keyboardpartner/esim_8266/docs/EPROM-Simulator_PEPS_(1985-05)_GERMAN.pdf

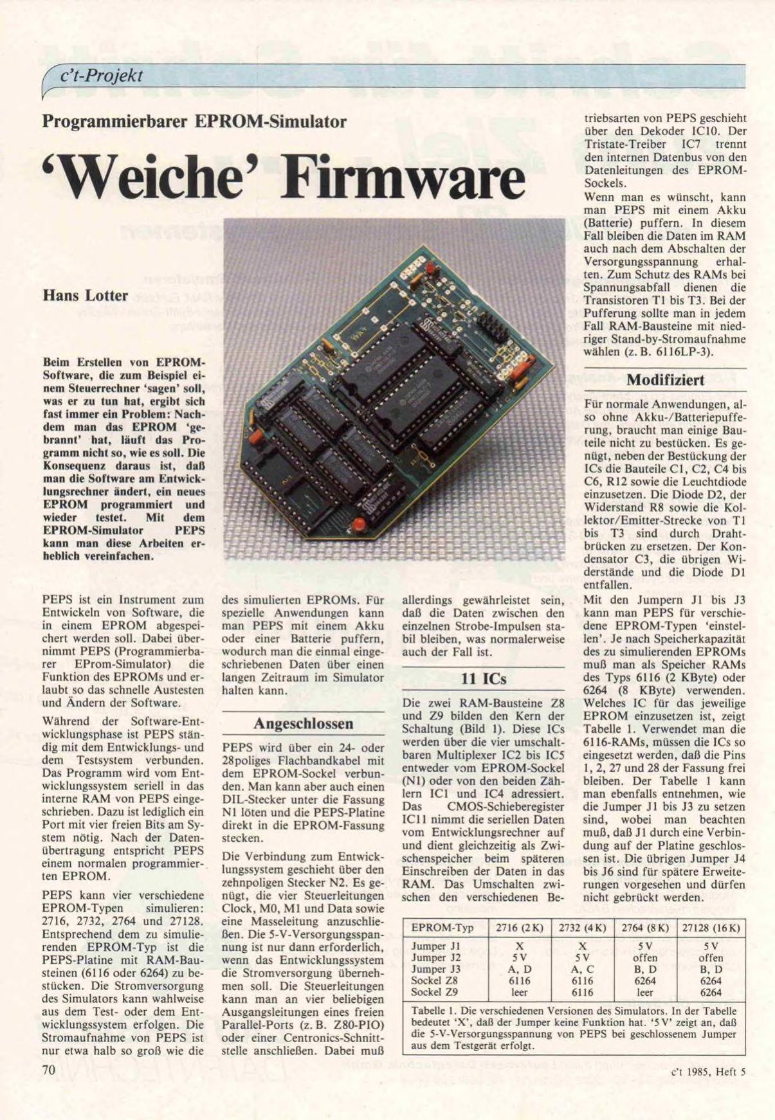
[picture p55: page 1]
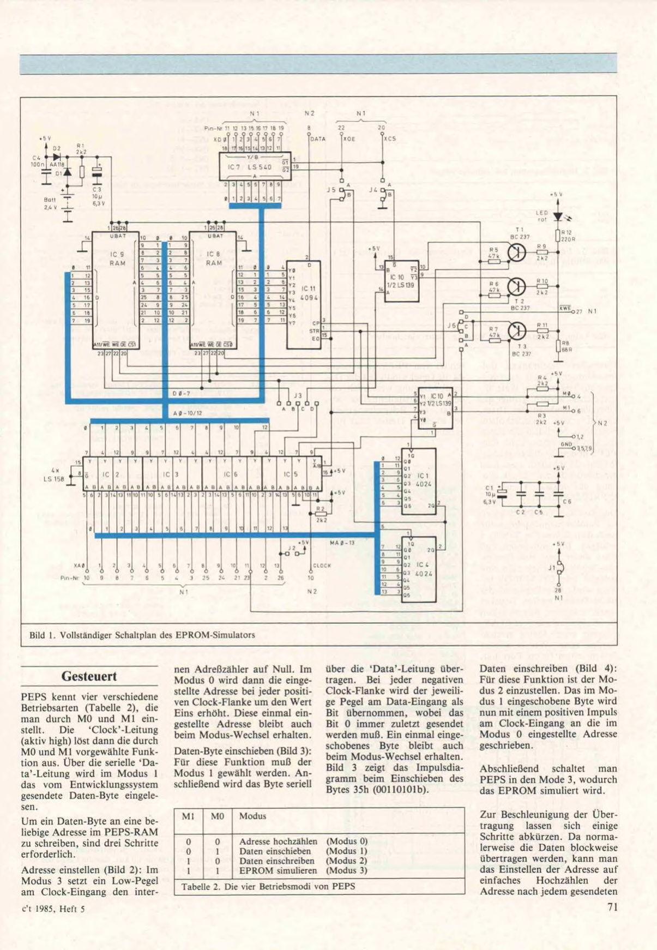
[picture p56: page 2]
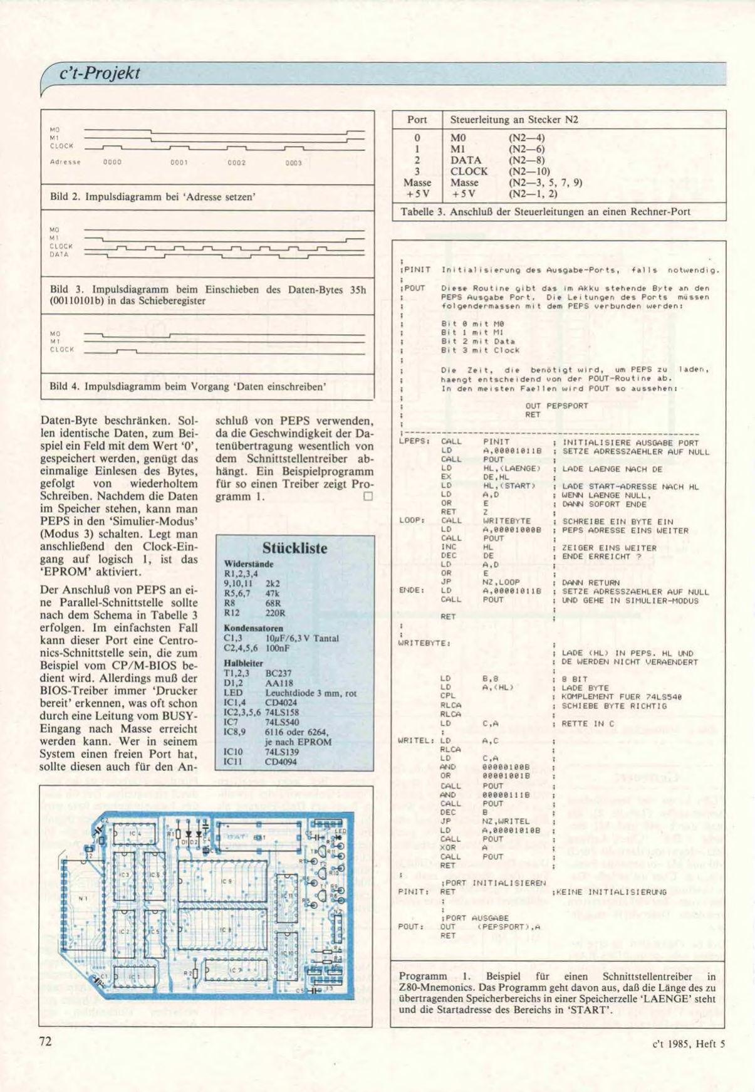
[picture p57: page 3]
