keyboardpartner/esim_8266/docs/2532-EPROM.gif

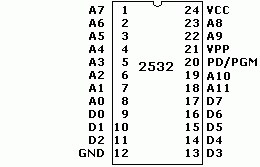
docs/2532-EPROM.gif
