keyboardpartner/esim_8266/docs/esim/pic02.jpg

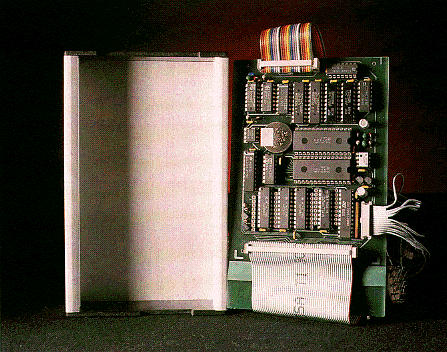
docs/esim/pic02.jpg
