keyboardpartner/esim_8266/docs/esim/pic04.jpg

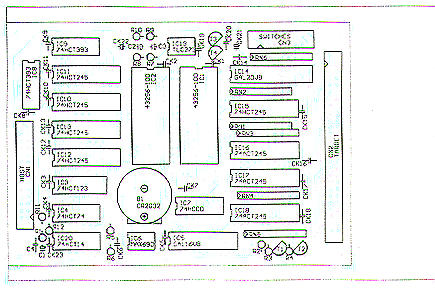
docs/esim/pic04.jpg
