keyboardpartner/esim_8266/pcb/MOJO/jtag_esp_simple_silk.pdf

D1
MD1

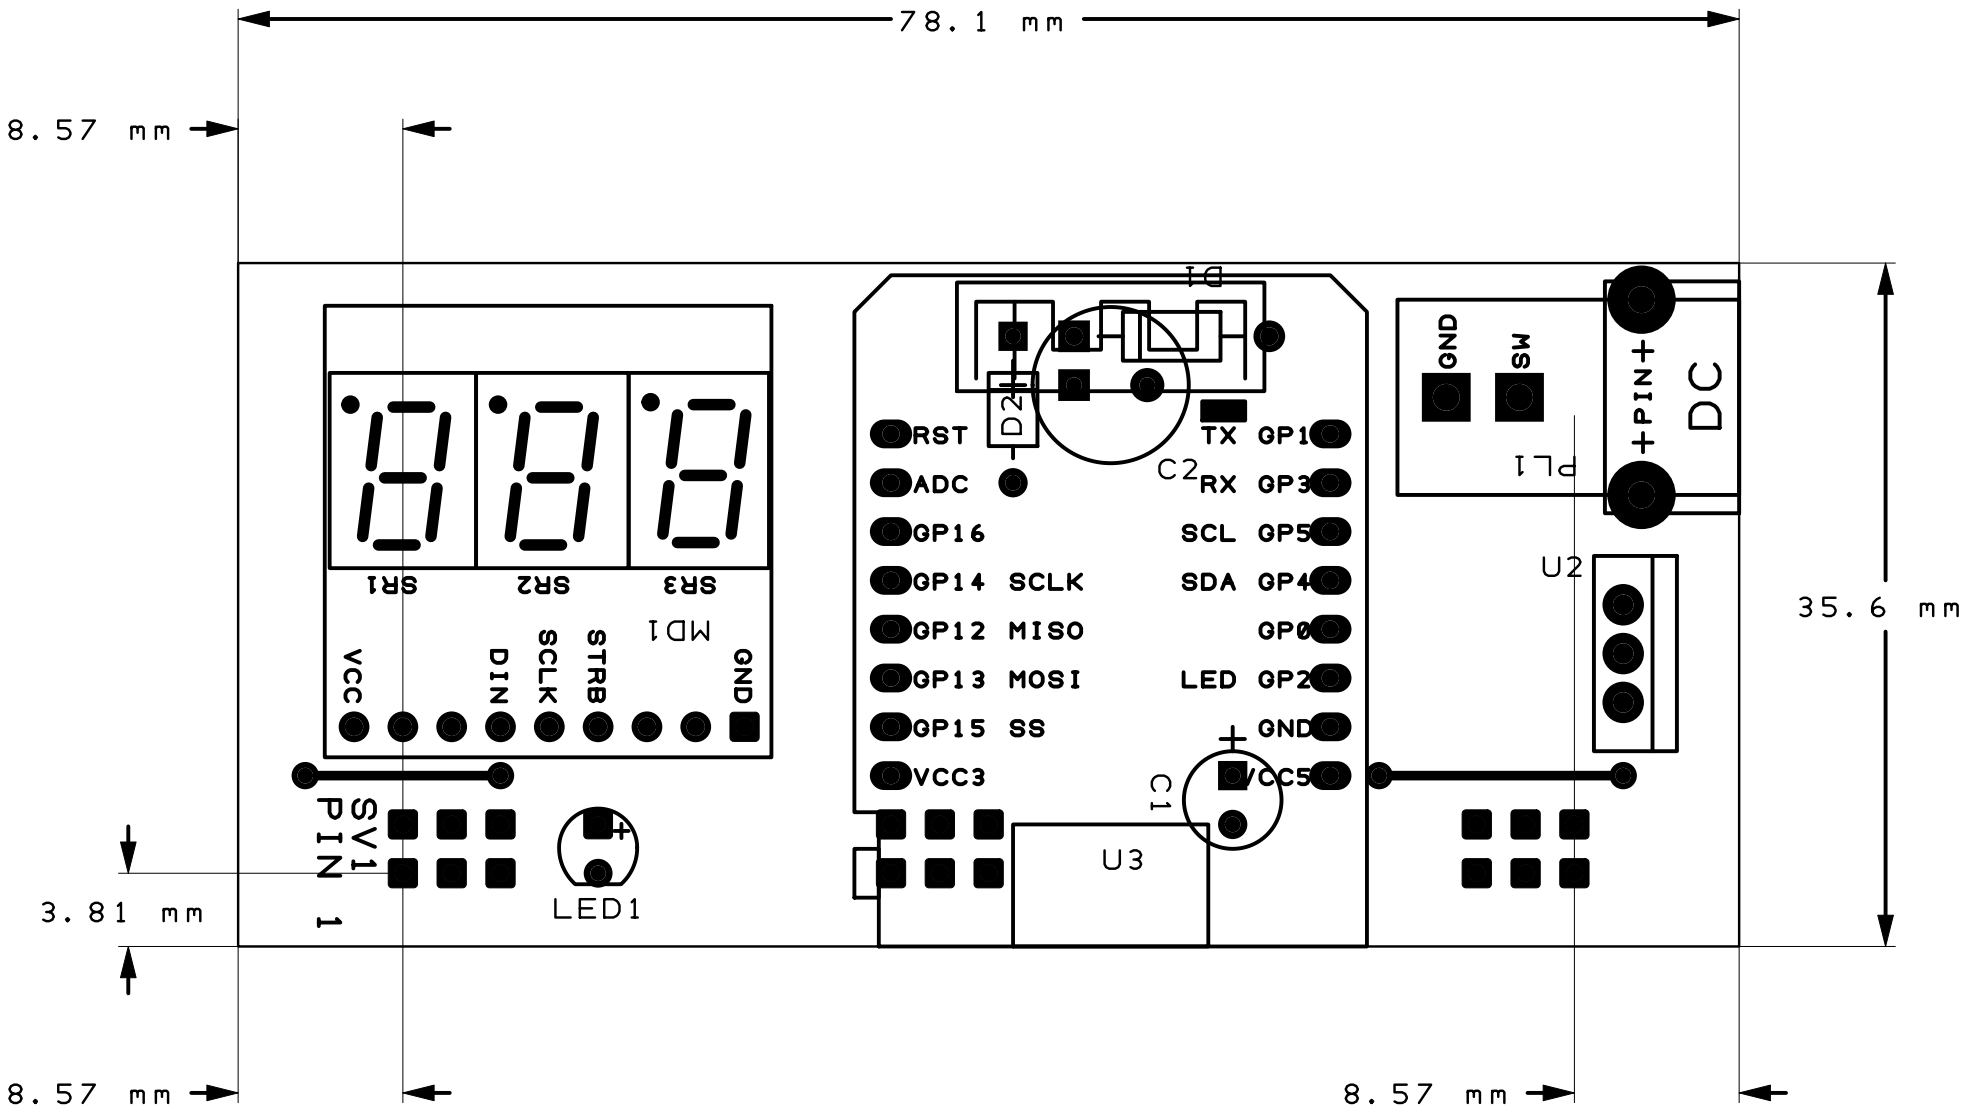
[picture p68: page 1]
LED1; LED1XZ1
