keyboardpartner/esim_8266/pcb/MOJO/jtag_esp_tft.pdf

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

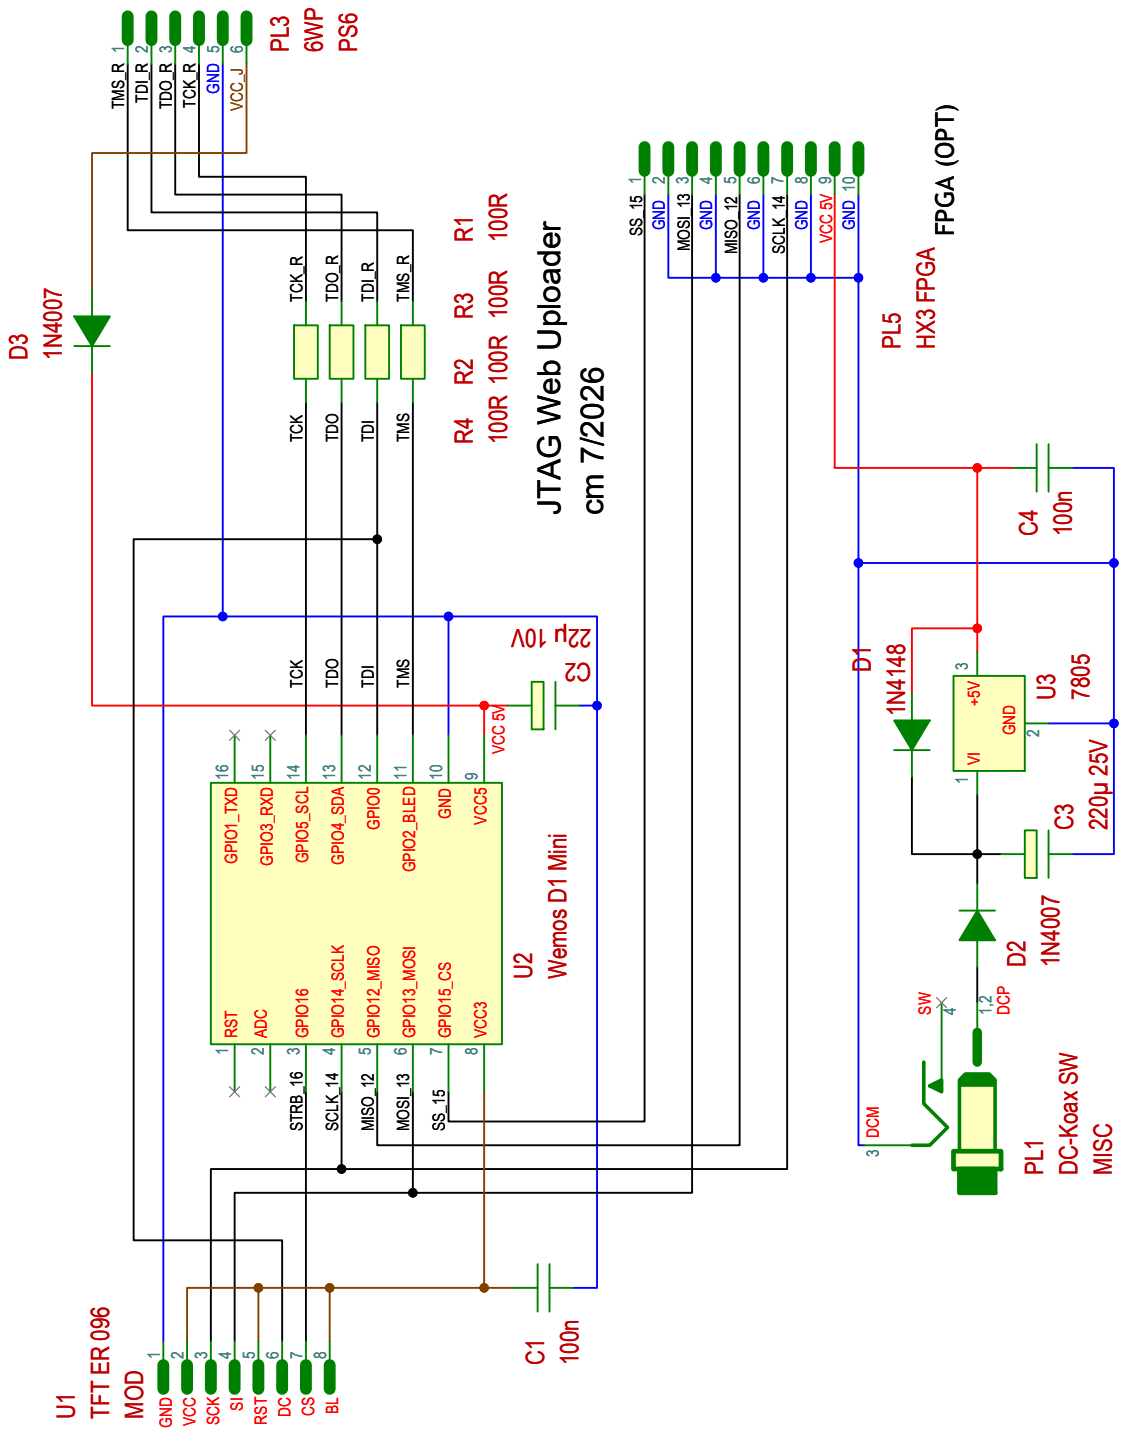
[picture p76: page 1]
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
