keyboardpartner/esim_8266/pcb/MOJO/jtag_esp_dil_cable_schem.pdf

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

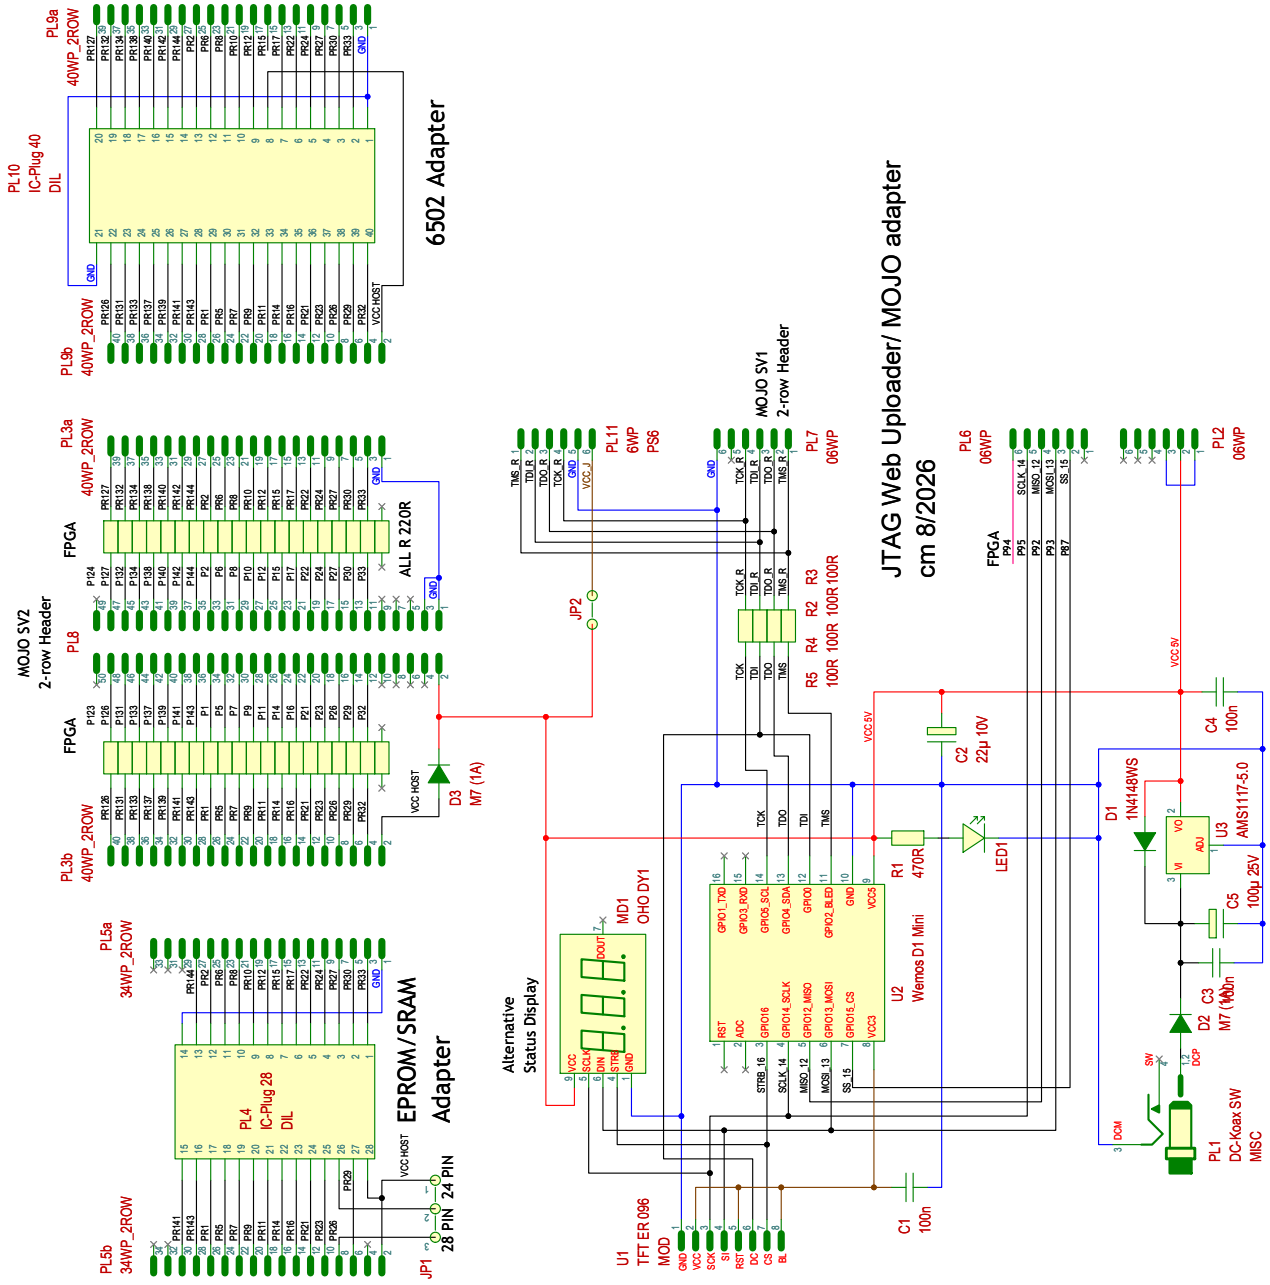
[picture p77: page 1]
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
