keyboardpartner/esim_8266/pcb/MOJO/jtag_esp_dil_cable_silk.pdf

PL4
PL5

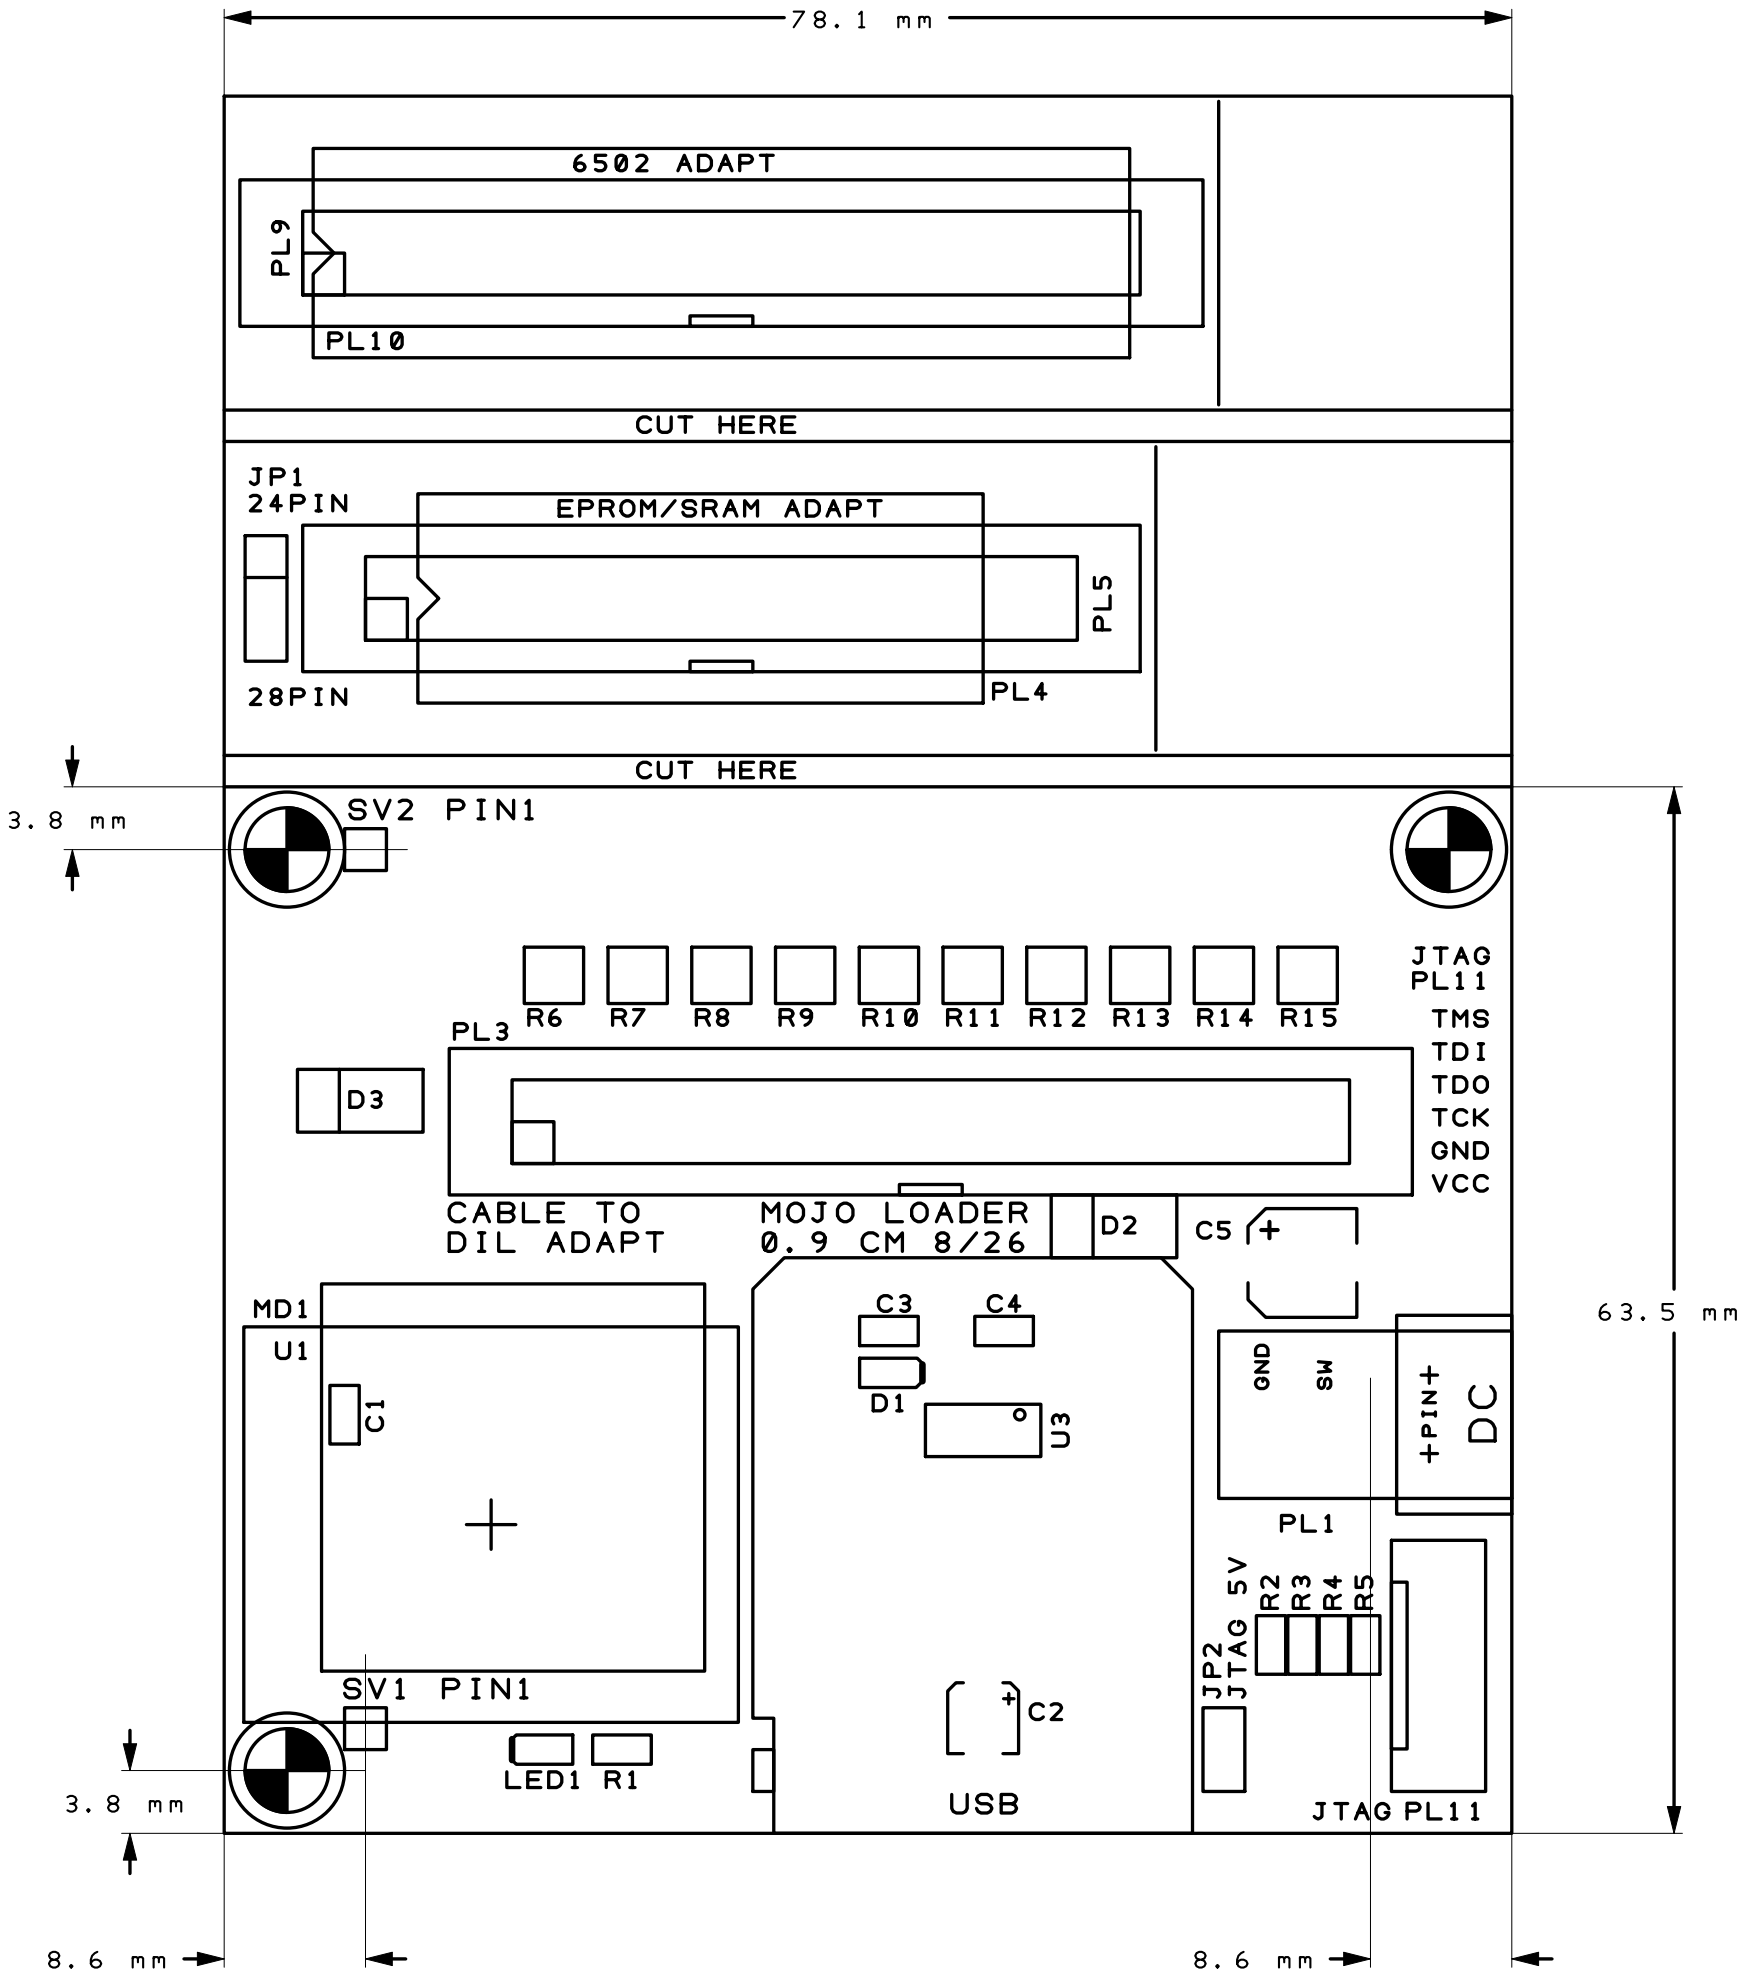
[picture p78: page 1]
