keyboardpartner/esim_8266/pcb/MOJO/jtag_esp_dil_cable_silk_btm.pdf

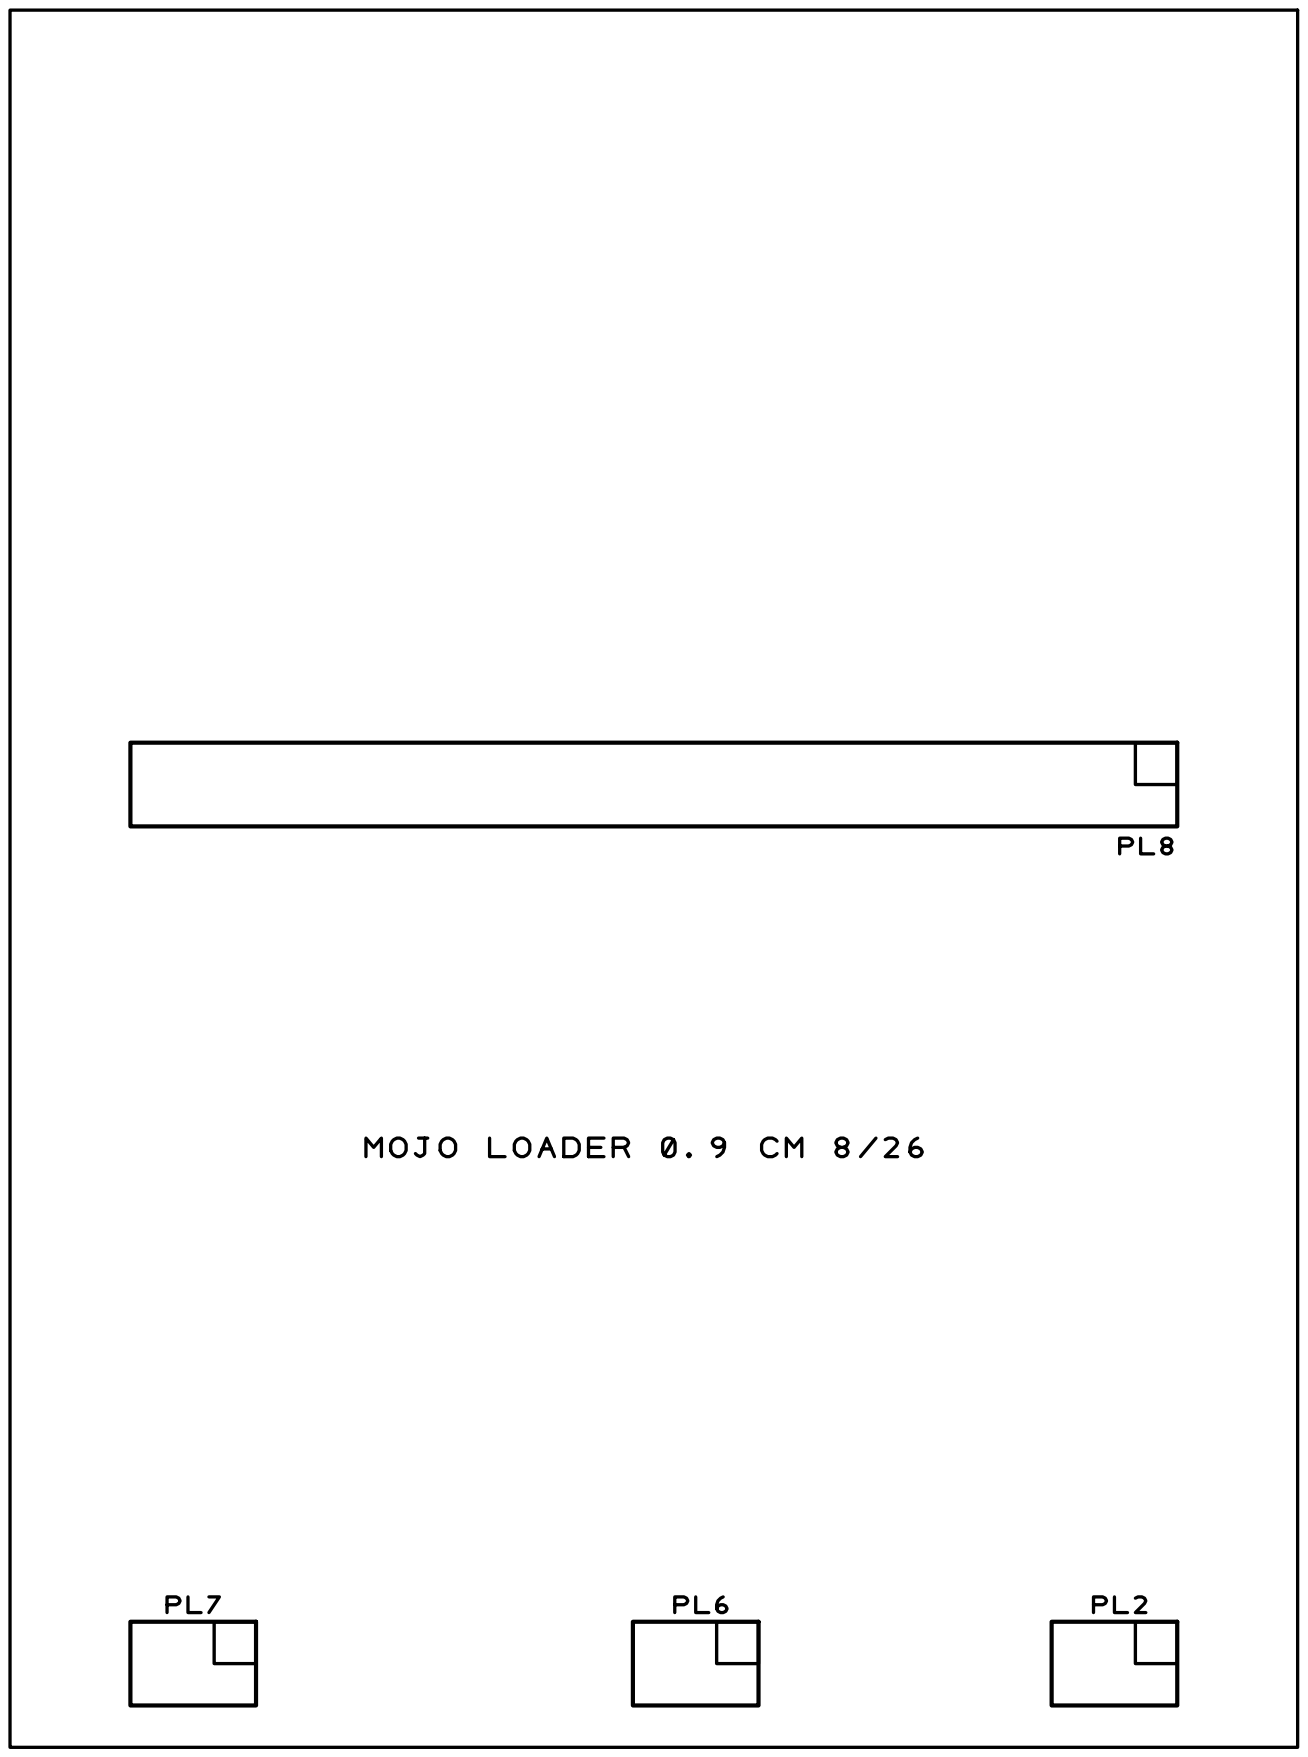
[picture p79: page 1]
