keyboardpartner/esim_8266/pcb/MOJO/mojo_eprom_adapter.pdf

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

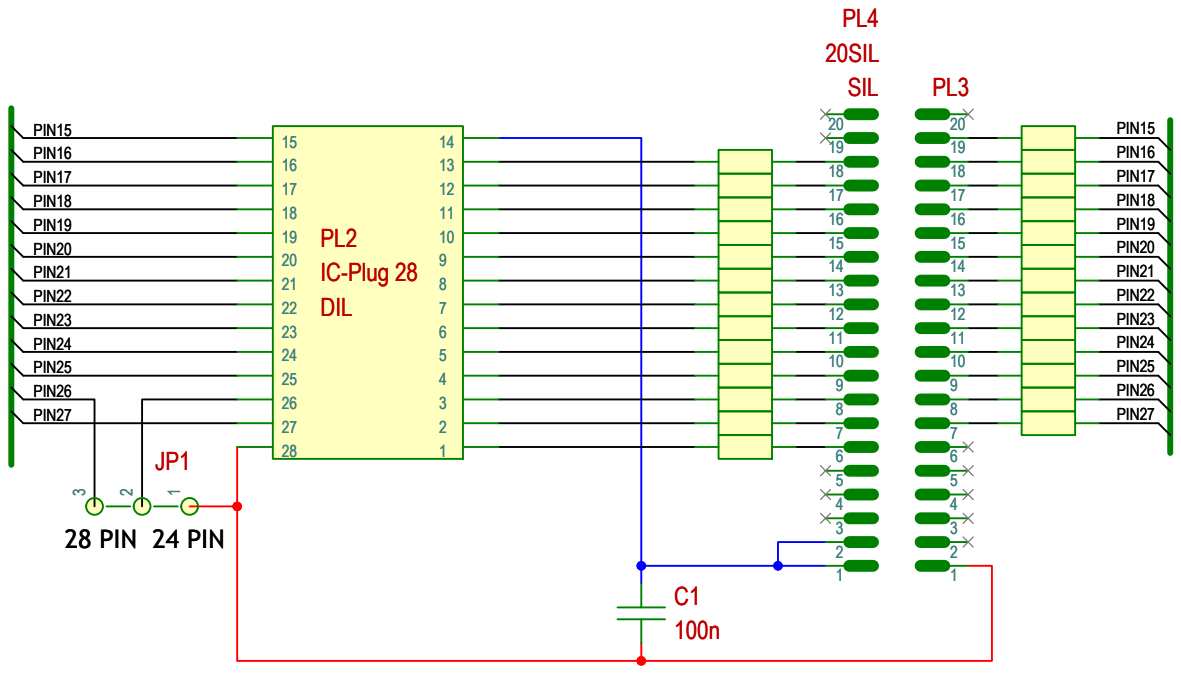
[picture p80: page 1]
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
