keyboardpartner/esim_8266/pcb/MOJO/jtag_esp_simple.pdf

D1
MD1

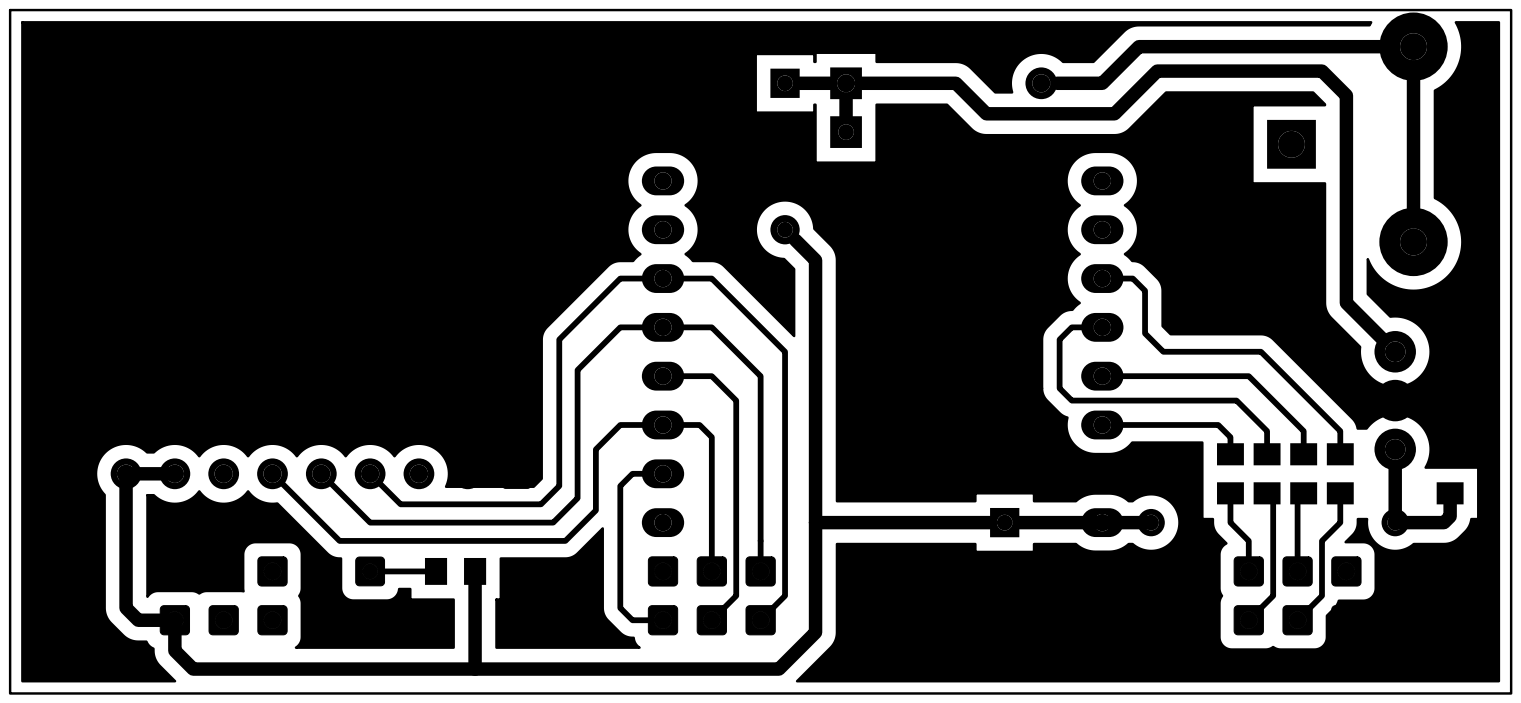
[picture p81: page 1]
