keyboardpartner/esim_8266/pcb/MOJO/jtag_esp_simple_botm.pdf

D1
MD1
