keyboardpartner/esim_8266/pcb/ESIM/esim_esp_pcb.pdf

PL2

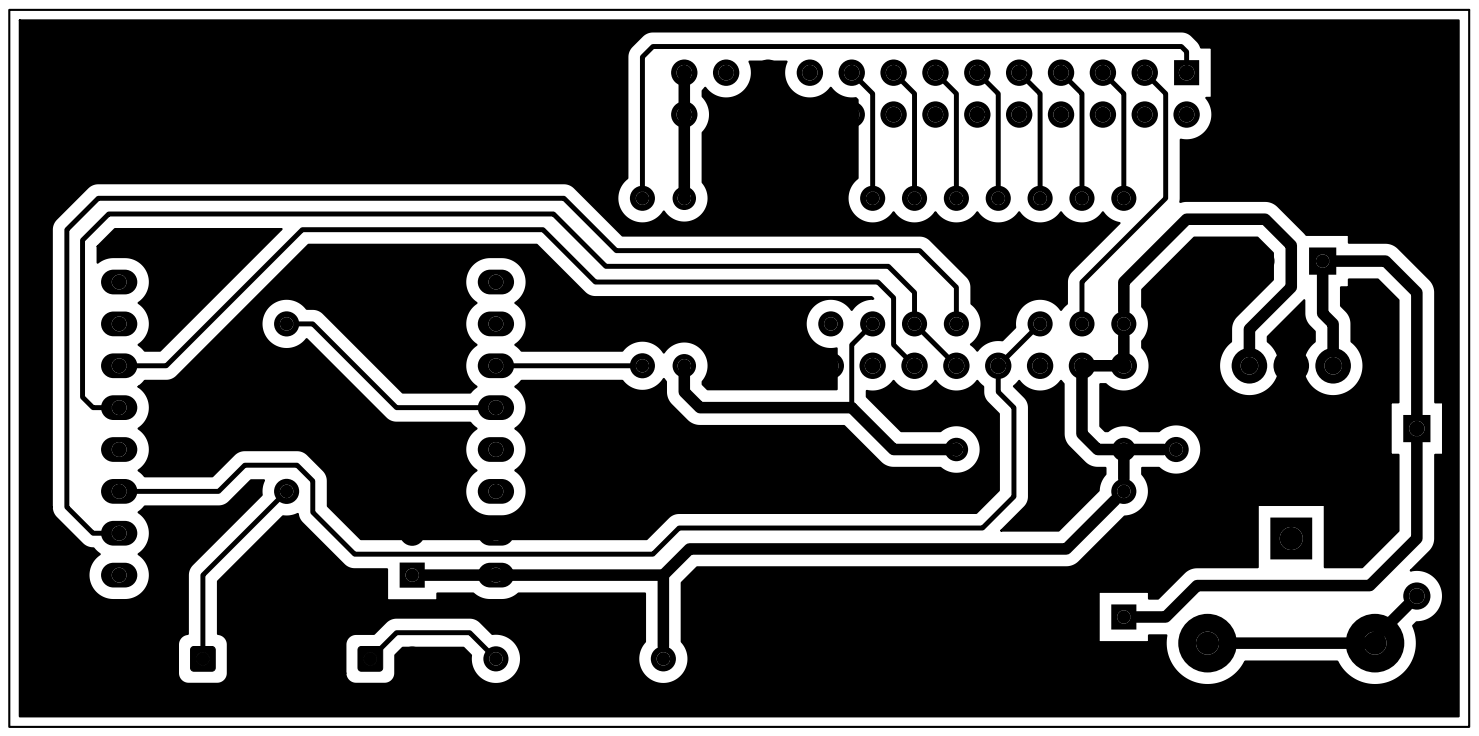
[picture p82: page 1]
