keyboardpartner/esim_8266/pcb/ESIM/esim_esp_silk.pdf

PL2

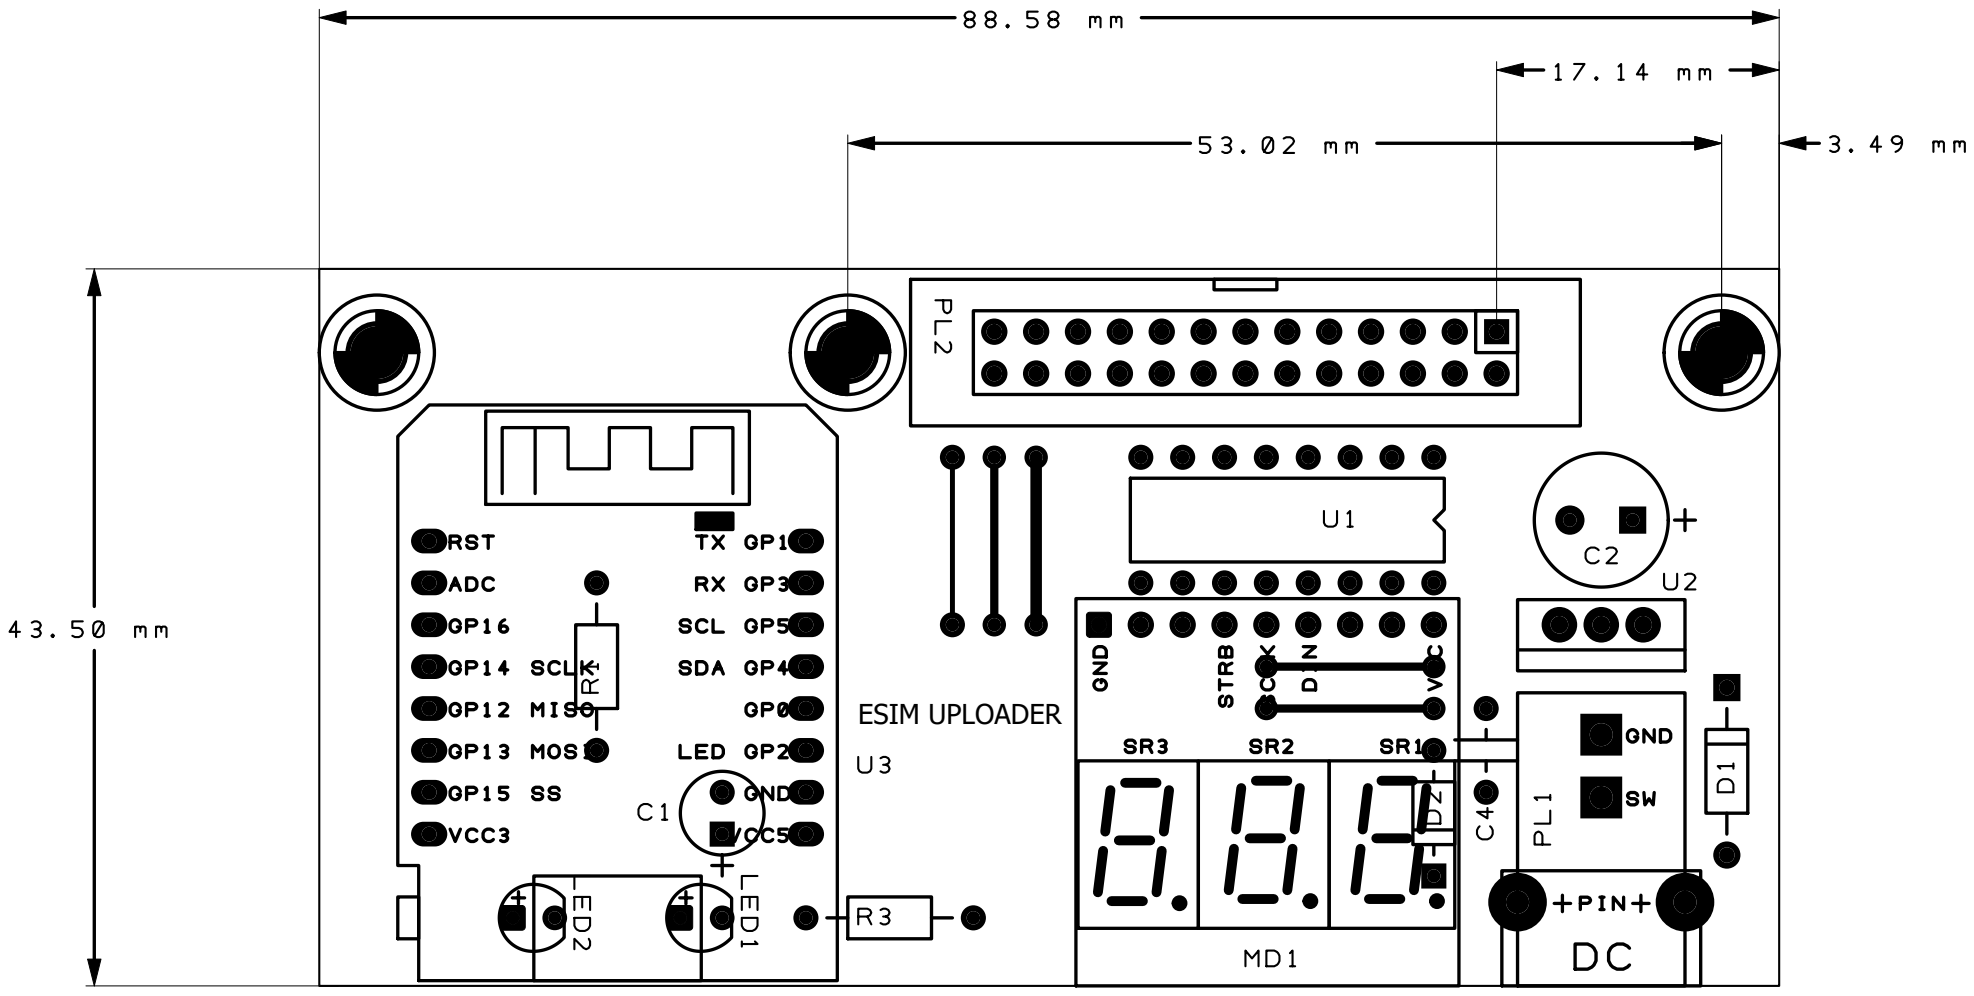
[picture p83: page 1]
