keyboardpartner/esim_8266/pcb/GODIL/godil_esp_silk.pdf

C1
MD1

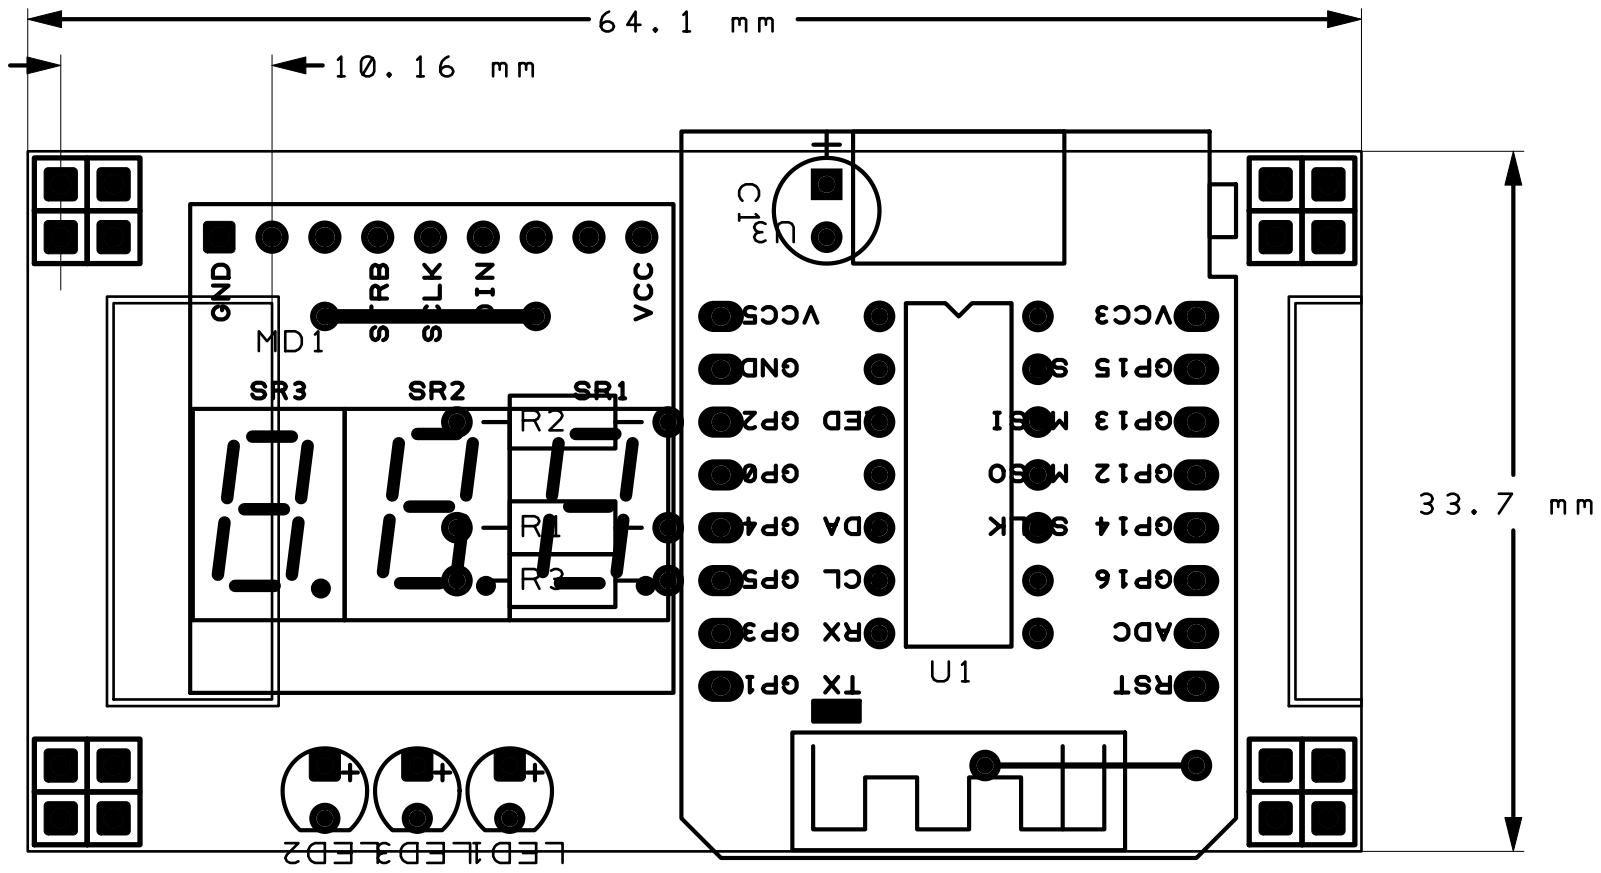
[picture p84: page 1]
