keyboardpartner/esim_8266/include/serial_cmd.h

#pragma once

// ##############################################################################
//
//      #####  ####### ######  ###    #    #           #####  #     # ######  
//     #     # #       #     #  #    # #   #          #     # ##   ## #     # 
//     #       #       #     #  #   #   #  #          #       # # # # #     # 
//      #####  #####   ######   #  #     # #          #       #  #  # #     # 
//           # #       #   #    #  ####### #          #       #     # #     # 
//     #     # #       #    #   #  #     # #          #     # #     # #     # 
//      #####  ####### #     # ### #     # #######     #####  #     # ######  
//                                                                                    
// ##############################################################################
// SERIAL COMMANDS
// ##############################################################################


// ##############################################################################
//
//     ### #     # ####### #######    #     # ####### #       ######  
//      #  ##    # #       #     #    #     # #       #       #     # 
//      #  # #   # #       #     #    #     # #       #       #     # 
//      #  #  #  # #####   #     #    ####### #####   #       ######  
//      #  #   # # #       #     #    #     # #       #       #       
//      #  #    ## #       #     #    #     # #       #       #       
//     ### #     # #       #######    #     # ####### ####### #       
//                                                                                  
// ##############################################################################
// SERIAL INFO AND HELP TEXT
// ##############################################################################

#include <Arduino.h>

void printIDcode() {
  #ifdef JTAG_SPARTAN6
    Serial.println("");
    printCenteredSerial(F("FPGA Info"));
    jtagCheckIDcode();
    Serial.printf("ID code: %08X\n", jtagIDcode);
    // Check for Xilinx ID code 0x0093 and print success or error message
    if (fpgaValid && fpgaConfigured) {
      Serial.println(F("FPGA configured successfully."));
    } else {
      Serial.println(F("FPGA configuration failed."));
      dy1message(F("Err"));
      drawMsgBox(F("FPGA"), F("ID Error"), DB_ERROR);
    }
    fpgaVersion = getFPGAversion();
    if ((fpgaVersion == 0xFFFFFFFF) || (fpgaVersion == 0x00000000)) {
      Serial.println(F("FPGA version read failed."));
      dy1message(F("Err"));
      drawMsgBox(F("FPGA"), F("Version Err"), DB_ERROR);
    } else {
      Serial.printf("FPGA version: %08X\n", fpgaVersion);
    }
    Serial.print(F("Emulation: "));
    Serial.println(kChipTypeNames[currentChipTypeIndex]);
    printDivLine();
   #endif
}

void printFileInfo() {
  const bool stagedExists = fsMounted && currentFilePath.length() > 0 && LittleFS.exists(currentFilePath);
  Serial.println("");
  printCenteredSerial(F("File Info"));
  Serial.print(F("LittleFS mounted: "));
  Serial.println(fsMounted ? F("Yes") : F("No"));
  Serial.print(F("FPGA Config: "));
  Serial.println(startupFpgaPath.length() ? startupFpgaPath : String(F("none")));
  Serial.print(F("Stream File: "));
  Serial.print(currentFilePath.length() ? currentFilePath : String(F("none")));
  Serial.println(stagedExists ? F(" OK") : F(" not found"));
  Serial.print(F("Start Addr: "));
  Serial.println(lastUploadStartAddr);
  Serial.print(F("Length: "));
  Serial.println(stagedFileBytes);
  printDivLine();
}

// Lists all LittleFS root directory entries on serial.
void listLittleFsEntries() {
  Serial.println("");
  if (!fsMounted) {
    Serial.println(F("ERROR: filesystem not mounted."));
    return;
  }
  Dir dir = LittleFS.openDir("/");
  size_t entryCount = 0;
  size_t totalBytes = 0;

  printCenteredSerial(F("Directory Info"));
  while (dir.next()) {
    const String path = normalizeFsPath(dir.fileName());
    const size_t bytes = dir.fileSize();
    Serial.print(path);
    Serial.print(F(" ("));
    Serial.print(bytes);
    Serial.println(F(" bytes)"));
    ++entryCount;
    totalBytes += bytes;
    delay(0); yield();
  }
  if (entryCount == 0) {
    Serial.println(F("  <empty>"));
  }
  Serial.print(F("Entries: "));
  Serial.print(entryCount);
  Serial.print(F(", total bytes: "));
  Serial.println(totalBytes);
  printDivLine();
}

void printWebInfo() {
  Serial.println("");
  printCenteredSerial(F("WiFi Info"));
  Serial.print(F("Wi-Fi mode: "));
  Serial.println(wifiModeLabel);
  Serial.print(F("Wi-Fi STA SSID: "));
  Serial.println(staSsid.length() ? staSsid : String(F("<empty>")));
  Serial.print(F("IP address: "));
  Serial.println(wifiIpAddress);
  Serial.print(F("AP SSID: "));
  Serial.println(kApSsid);
  printDivLine();
}


// ##############################################################################
//
//     #     # ####### #       ######  ####### ######   #####  
//     #     # #       #       #     # #       #     # #     # 
//     #     # #       #       #     # #       #     # #       
//     ####### #####   #       ######  #####   ######   #####  
//     #     # #       #       #       #       #   #         # 
//     #     # #       #       #       #       #    #  #     # 
//     #     # ####### ####### #       ####### #     #  #####  
//                                                                                    
// ##############################################################################
// SERIAL COMMAND HELPER FUNCTIONS
// ##############################################################################
                                                          
#if defined(GODIL_SPI) || defined(JTAG_SPARTAN6)
void hexdumpInputBytes256(uint32_t startAddr) {
  // Hex dump 256 bytes from device starting at startAddr.
  startBlockTransfer(startAddr);
  for (uint16_t rowStart = 0; rowStart < 256; rowStart += 16) {
    char line[96];
    int lineLen = snprintf(line, sizeof(line), "%06lX: ", static_cast<unsigned long>(startAddr + rowStart));
    for (uint8_t i = 0; i < 16; ++i) {
      const uint8_t value = inputByte();
      lineLen += snprintf(line + lineLen, sizeof(line) - lineLen, "%02X ", value);
    }

    if (lineLen > 0 && line[lineLen - 1] == ' ') {
      line[lineLen - 1] = '\0';
    }
    Serial.println(line);

    if ((rowStart & 0x007F) == 0) {
      delay(0); yield();
    }
  }
  stopBlockTransfer();
}
#endif

void printSerialCommandsInfo() {
  Serial.println("");
  printCenteredSerial(F("Serial Commands"));
  #ifdef JTAG_SPARTAN6
    Serial.println(F("c: Configurate FPGA with last/staged .bit file"));
    Serial.println(F("o: List chip types and select emulation mode"));
  #endif
  #if defined(GODIL_SPI) || defined(JTAG_SPARTAN6)
    Serial.println(F("d<start><CR>: Hexdump of 256 bytes from device"));
    Serial.println(F("j<filename,start,len><CR>: dump EPROM to file"));
  #endif
  Serial.println(F("e: Erase EPROM"));
  Serial.println(F("h: Print web/status info and this help text"));
  Serial.println(F("i: Print file debug info"));
  Serial.println(F("l: List LittleFS directory entries"));
  Serial.println(F("t: Test SPI transfer"));
  Serial.println(F("r: Replay last/staged file"));
  printDivLine();
  Serial.println(F("a<start><CR>: Set start address for next serial upload"));
  Serial.println(F("n<filename><CR>: Set filename for next serial upload"));
  Serial.println(F("u<lenLo><lenHi><data...><cksLo><cksHi>: Framed binary upload"));
  Serial.println(F("x: Print \"Ready.\" for handshaking with serial uploader"));
  printDivLine();
  Serial.println(F("w<ssid><CR>: Set STA Wi-Fi SSID"));
  Serial.println(F("p<password><CR>: Set STA Wi-Fi password"));
  Serial.println();
  Serial.println(F("Note: start/len accept decimal or 0x-prefixed hex"));
  printDivLine();
}  

// Reads one serial byte with timeout to support robust framed transfers.
bool readSerialByteWithTimeout(uint8_t &outByte, uint32_t timeoutMs) {
  const uint32_t startMs = millis();
  while ((millis() - startMs) < timeoutMs) {
    if (Serial.available() > 0) {
      outByte = static_cast<uint8_t>(Serial.read());
      return true;
    }
    delay(0); yield();
  }
  return false;
}

// Reads an ASCII filename terminated by CR for the next serial upload.
bool readSerialFilename(String &filenameOut) {
  String rawName;
  while (true) {
    uint8_t nextByte = 0;
    if (!readSerialByteWithTimeout(nextByte, kSerialUploadTimeoutMs*25U)) {
      return false;
    }
    if (nextByte == '\r') {
      filenameOut = sanitizeUploadFilename(rawName);
      return true;
    }
    if (nextByte == '\n') {
      continue;
    }
    rawName += static_cast<char>(nextByte);
    if (rawName.length() > kMaxFsPathLength * 2) {
      rawName.remove(kMaxFsPathLength * 2);
    }
  }
}

// Reads one ASCII line terminated by CR from serial input.
bool readSerialLine(String &lineOut, uint32_t timeoutMs) {
  String line;
  while (true) {
    uint8_t nextByte = 0;
    if (!readSerialByteWithTimeout(nextByte, timeoutMs)) {
      return false;
    }
    if (nextByte == '\r') {
      lineOut = line;
      return true;
    }
    if (nextByte == '\n') {
      continue;
    }
    line += static_cast<char>(nextByte);
    if (line.length() > 128) {
      line.remove(128);
    }
  }
}

// Parses decimal or 0x-prefixed hexadecimal unsigned values.
bool parseUnsignedValue(const String &text, uint32_t &valueOut) {
  String token = text;
  token.trim();
  if (token.length() == 0) {
    return false;
  }
  char *endPtr = nullptr;
  const unsigned long parsed = std::strtoul(token.c_str(), &endPtr, 0);
  if (endPtr == token.c_str() || *endPtr != '\0') {
    return false;
  }
  valueOut = static_cast<uint32_t>(parsed);
  return true;
}

// Parses serial dump command format: filename,start,len
bool parseDumpCommandArgs(const String &line, String &filenameOut, uint32_t &startAddrOut,
                          uint16_t &lenOut) {
  String argLine = line;
  argLine.trim();
  const int comma1 = argLine.indexOf(',');
  const int comma2 = (comma1 >= 0) ? argLine.indexOf(',', comma1 + 1) : -1;
  if (comma1 <= 0 || comma2 <= comma1 + 1) {
    return false;
  }
  const String filenameRaw = argLine.substring(0, comma1);
  const String startRaw = argLine.substring(comma1 + 1, comma2);
  const String lenRaw = argLine.substring(comma2 + 1);

  uint32_t parsedStart = 0;
  uint32_t parsedLen = 0;
  if (!parseUnsignedValue(startRaw, parsedStart) || !parseUnsignedValue(lenRaw, parsedLen)) {
    return false;
  }
  if (parsedLen == 0 || parsedLen > 0xFFFFUL) {
    return false;
  }
  String cleanName = sanitizeUploadFilename(filenameRaw);
  if (cleanName.length() == 0) {
    return false;
  }
  filenameOut = cleanName;
  startAddrOut = parsedStart;
  lenOut = static_cast<uint16_t>(parsedLen);
  return true;
}

                                                    
// ##############################################################################
//
//     #     # ######  #       #######    #    ######  
//     #     # #     # #       #     #   # #   #     # 
//     #     # #     # #       #     #  #   #  #     # 
//     #     # ######  #       #     # #     # #     # 
//     #     # #       #       #     # ####### #     # 
//     #     # #       #       #     # #     # #     # 
//      #####  #       ####### ####### #     # ######  
//                                                                                    
// ##############################################################################
// Handles serial upload command.
// ##############################################################################


// Usage: 'u' + lenLo,lenHi + payload + cksLo,cksHi; ACK after len, each 128B, checksum.
void processSerialUploadCommand() {
  if (!fsMounted) {
    Serial.println(F("ERROR: filesystem not mounted."));
    return;
  }

  uint8_t lenLo = 0;
  uint8_t lenHi = 0;
  if (!readSerialByteWithTimeout(lenLo, kSerialUploadTimeoutMs) ||
      !readSerialByteWithTimeout(lenHi, kSerialUploadTimeoutMs)) {
    Serial.write(kSerialNakByte);
    Serial.println(F("ERROR: timeout while reading length word."));
    return;
  }

  const uint16_t payloadLength = static_cast<uint16_t>(lenLo) |
                                 (static_cast<uint16_t>(lenHi) << 8);
  if (payloadLength == 0) {
    Serial.println(F("ERROR: payload length is zero."));
    return;
  }

  if (payloadLength > kMaxBytesToTransfer[currentChipTypeIndex]) {
    Serial.print(F("ERROR: payload exceeds limit "));
    Serial.println(kMaxBytesToTransfer[currentChipTypeIndex]);
    return;
  }

  // ACK command and length word, signaling sender to start payload transmission.
  Serial.write(kSerialAckByte);

  if (uploadStagingFile) {
    uploadStagingFile.close();
  }
  currentUploadFsError = false;
  uploadInProgress = true;
  setUploadLed(true);
  const String requestedFilename = pendingSerialFilename;
  pendingSerialFilename = String();
  if (requestedFilename.length() > 0) {
    currentFilePath = makeWebUploadFilePath(requestedFilename);
    lastFilename = requestedFilename;
  } else {
    currentFilePath = makeWebUploadFilePath(F("serial_upload.bin"));
    lastFilename = baseNameFromPath(currentFilePath);
  }
  DPRINT(F("Serial upload path: "));
  DPRINTLN(currentFilePath);
  stagedFileBytes = 0;
  streamOffset = 0;
  clearDataBus();

  LittleFS.remove(currentFilePath);
  uploadStagingFile = LittleFS.open(currentFilePath, "w");
  if (!uploadStagingFile) {
    currentUploadFsError = true;
    uploadInProgress = false;
    setUploadLed(false);
    Serial.println(F("ERROR: failed to open staging file."));
    return;
  }

  uint16_t calculatedChecksum = 0;

  for (uint16_t i = 0; i < payloadLength; ++i) {
    uint8_t dataByte = 0;
    if (!readSerialByteWithTimeout(dataByte, kSerialUploadTimeoutMs)) {
      uploadStagingFile.close();
      LittleFS.remove(currentFilePath);
      stagedFileBytes = 0;
      lastFileBytes = 0;
      currentUploadFsError = true;
      uploadInProgress = false;
      setUploadLed(false);
      Serial.write(kSerialNakByte);
      Serial.println(F("ERROR: timeout waiting for data byte."));
      return;
    }

    const size_t written = uploadStagingFile.write(&dataByte, 1);
    if (written != 1) {
      uploadStagingFile.close();
      LittleFS.remove(currentFilePath);
      stagedFileBytes = 0;
      lastFileBytes = 0;
      currentUploadFsError = true;
      uploadInProgress = false;
      setUploadLed(false);
      Serial.println(F("ERROR: write failed."));
      return;
    }

    ++stagedFileBytes;
    calculatedChecksum = static_cast<uint16_t>(calculatedChecksum + dataByte);

    const uint16_t receivedBytes = static_cast<uint16_t>(i + 1);
    if ((receivedBytes % kSerialAckChunkBytes) == 0 || receivedBytes == payloadLength) {
      Serial.write(kSerialAckByte);
    }

    if ((i & 0x1F) == 0) {
      delay(0); yield();
    }
  }

  uint8_t cksLo = 0;
  uint8_t cksHi = 0;
  if (!readSerialByteWithTimeout(cksLo, kSerialUploadTimeoutMs) ||
      !readSerialByteWithTimeout(cksHi, kSerialUploadTimeoutMs)) {
    uploadStagingFile.close();
    LittleFS.remove(currentFilePath);
    stagedFileBytes = 0;
    lastFileBytes = 0;
    currentUploadFsError = true;
    uploadInProgress = false;
    setUploadLed(false);
    Serial.write(kSerialNakByte);
    Serial.println(F("ERROR: timeout while reading checksum word."));
    return;
  }

  const uint16_t receivedChecksum = static_cast<uint16_t>(cksLo) |
                                    (static_cast<uint16_t>(cksHi) << 8);

  if (receivedChecksum != calculatedChecksum) {
    uploadStagingFile.close();
    LittleFS.remove(currentFilePath);
    stagedFileBytes = 0;
    lastFileBytes = 0;
    currentUploadFsError = true;
    uploadInProgress = false;
    setUploadLed(false);
    Serial.write(kSerialNakByte);
    Serial.print(F("ERROR: checksum mismatch, expected="));
    Serial.print(calculatedChecksum);
    Serial.print(F(", received="));
    Serial.println(receivedChecksum);
    return;
  }

  // ACK checksum receipt only when checksum is valid.
  Serial.write(kSerialAckByte);

  uploadStagingFile.close();
  lastFileBytes = stagedFileBytes;
  uploadInProgress = false;
  setUploadLed(false);
  lastFilename = baseNameFromPath(currentFilePath);
  // lastUploadStartAddr is already set when processing the 'a' command.
  if (isBitstreamFilePath(currentFilePath)) {
    startupFpgaPath = normalizeFsPath(currentFilePath);
    lastUploadStartAddr = 0;
  }
  if (!saveFileSettingsForFile(currentFilePath, lastUploadStartAddr)) {
    Serial.println(F("ERROR: failed to save file settings metadata."));
  }
  if (!saveGlobalSettings()) {
    Serial.println(F("ERROR: failed to save global settings."));
  }
  if (!startPlaybackFromStaging(lastUploadStartAddr, currentFilePath)) {
    currentUploadFsError = true;
    Serial.println(F("ERROR: failed to send staged file."));
    return;
  }
  Serial.print(F("Serial upload OK: bytes="));
  Serial.println(stagedFileBytes);
  Serial.println(F("Ready."));
}

// ##############################################################################
//
//     ######  ######  #######  #####  #######  #####   #####  
//     #     # #     # #     # #     # #       #     # #     # 
//     #     # #     # #     # #       #       #       #       
//     ######  ######  #     # #       #####    #####   #####  
//     #       #   #   #     # #       #             #       # 
//     #       #    #  #     # #     # #       #     # #     # 
//     #       #     # #######  #####  #######  #####   #####  
//                                                             
// ##############################################################################
// Processes single-character serial commands (r, c, i, x, n, u, and d).
// ##############################################################################

void processSerialCommands() {
  String dumpLine;
  String optionString;
  String filename;
  String wifiValue;
  #if defined(GODIL_SPI) || defined(JTAG_SPARTAN6)
    static uint32_t startAddr = 0;
    uint16_t len = 0;
  #endif
  while (Serial.available() > 0) {
    const char cmd = static_cast<char>(Serial.read());
    switch (cmd) {
      case 'a':
      case 'A':
        Serial.print(F("\rStart address (dec/0x): "));
        if (!readSerialLine(optionString, kSerialUploadTimeoutMs * 25U)) {
          Serial.println(F("\rERROR: timeout while reading start address."));
          break;
        }
        optionString.trim();
        if (optionString.length() > 0 && !parseUnsignedValue(optionString, lastUploadStartAddr)) {
          Serial.println(F("\rERROR: invalid start address. Use decimal or 0x-prefixed hex."));
          break;
        }
        Serial.print(F("Start address set to 0x"));
        Serial.println(lastUploadStartAddr, HEX);
        break;
      #ifdef JTAG_SPARTAN6
        case 'c':
        case 'C':
          // config SPARTAN 6 FPGA via JTAG (only available in JTAG_SPARTAN6 mode)
          Serial.write('\r');
          dy1message(F("cfg"));
          drawStringBox("FPGA Cfg", startupFpgaPath, 0);
          jtagConfigure(startupFpgaPath);
          printIDcode();
          break;
      #endif
      case 'e':
      case 'E':
        Serial.write('\r');
        eraseEPROM();
        break;
      case 'r':
      case 'R':
        Serial.print(F("\rReplay...  "));
        startPlaybackFromStaging(lastUploadStartAddr, currentFilePath);
        break;
      case 'i':
      case 'I':
        printFileInfo();
        break;
      case 'd':
      case 'D':
        #if defined(GODIL_SPI) || defined(JTAG_SPARTAN6)
          Serial.print(F("\rDump from addr: "));
          if (!readSerialLine(optionString, kSerialUploadTimeoutMs * 25U)) {
            Serial.println(F("\rERROR: timeout while reading hexdump start address."));
            break;
          }
          optionString.trim();
          if (optionString.length() > 0 && !parseUnsignedValue(optionString, startAddr)) {
            Serial.println(F("\rERROR: invalid start address. Use decimal or 0x-prefixed hex."));
            break;
          }

          hexdumpInputBytes256(startAddr);
          startAddr += 256;
        #else
          Serial.println(F("\rERROR: command d is only available in FPGA mode."));
        #endif
        break;
      case 'o':
      case 'O':
        #if defined(GODIL_SPI) || defined(JTAG_SPARTAN6)
          // List chip types and prompt for selection (only available in FPGA mode)
          Serial.println(F("\rAvailable chip types:"));
          for (uint32_t i = 0; i < kChipTypeCount; ++i) {
            Serial.write(' ');
            if (i < 10) {
              Serial.write(' ');
            }
            Serial.print(i);
            Serial.print(F(": "));
            Serial.print(kChipTypeNames[i]);
            if (i == currentChipTypeIndex) {
              Serial.print(F(" (active)"));
            }
            Serial.println();
          }
          Serial.print(F("Chip type (0.."));
          Serial.print(kChipTypeCount - 1);
          Serial.print(F("): "));
          if (!readSerialLine(optionString, kSerialUploadTimeoutMs * 25U)) {
            Serial.println(F("\rERROR: timeout while reading chip type."));
            break;
          }
          optionString.trim();
          if (optionString.length() > 0 && !parseUnsignedValue(optionString, currentChipTypeIndex)) {
            Serial.println(F("\rERROR: invalid chip type. Use decimal or 0x-prefixed hex."));
            break;
          }
          Serial.print(F("Emulation set to "));
          Serial.println(kChipTypeNames[currentChipTypeIndex]);
          outputChipType(currentChipTypeIndex);
          saveGlobalSettings();
        #else
          Serial.println(F("\rERROR: command o is only available in FPGA mode."));
        #endif
        break;
      case 'l':
      case 'L':
        listLittleFsEntries();
        break;
      case 'h':
      case 'H':
        #ifdef JTAG_SPARTAN6
          printIDcode();
        #endif
        printWebInfo();
        printSerialCommandsInfo();
        break;
      case 'x':
      case 'X':
        Serial.println();
        Serial.println(F("Ready."));
        break;
      case 't':
      case 'T':
        Serial.write('\r');
        testSPItransfer();
        dy1test();
        Serial.println(F("Ready."));
       break;
      case 'n':
      case 'N':
        if (!readSerialFilename(filename)) {
          pendingSerialFilename = String();
          Serial.write(kSerialNakByte);
          Serial.println(F("\rERROR: timeout while reading filename."));
        } else {
          pendingSerialFilename = filename;
          Serial.write(kSerialAckByte);
        }
        break;
      case 'w':
      case 'W':
        Serial.print(F("\rWi-Fi SSID="));
        if (!readSerialLine(wifiValue, kSerialUploadTimeoutMs * 25U)) {
          Serial.println(F("\rERROR: timeout while reading SSID."));
          continue;
        }
        wifiValue.trim();
        if (wifiValue.length() == 0) {
          Serial.println(F("ERROR: SSID must not be empty."));
          continue;
        }
        staSsid = wifiValue;
        if (!saveGlobalSettings()) {
          Serial.println(F("\rERROR: failed to save Wi-Fi SSID."));
          continue;
        }
        Serial.print(F("Wi-Fi SSID saved: "));
        Serial.println(staSsid);
        break;
      case 'p':
      case 'P':
        Serial.print(F("\rWi-Fi Password="));
        if (!readSerialLine(wifiValue, kSerialUploadTimeoutMs * 25U)) {
          Serial.println(F("\rERROR: timeout while reading password."));
          continue;
        }
        staPassword = wifiValue;
        if (!saveGlobalSettings()) {
          Serial.println(F("\rERROR: failed to save Wi-Fi password."));
          continue;
        }
        Serial.println(F("\rWi-Fi password saved."));
        break;
      case 'u':
      case 'U':
        processSerialUploadCommand();
        break;
      case 'j':
      case 'J':
        #if defined(GODIL_SPI) || defined(JTAG_SPARTAN6)
          if (!readSerialLine(dumpLine, kSerialUploadTimeoutMs * 25U)) {
            Serial.write(kSerialNakByte);
            Serial.println(F("\rERROR: timeout while reading dump arguments."));
            continue;
          }

          if (!parseDumpCommandArgs(dumpLine, filename, startAddr, len)) {
            Serial.write(kSerialNakByte);
            Serial.println(F("\rERROR: invalid dump syntax. Use d<filename,start,len><CR>"));
            continue;
          }

          if (uploadInProgress) {
            Serial.write(kSerialNakByte);
            Serial.println(F("\rERROR: dump blocked while upload is active."));
            continue;
          }

          if (!writeEPROMtoFile(filename, startAddr, len)) {
            Serial.write(kSerialNakByte);
            Serial.println(F("\rERROR: EPROM dump failed."));
            continue;
          }

          lastFilename = baseNameFromPath(filename);
          lastFileBytes = len;
          Serial.write(kSerialAckByte);
          Serial.print(F("Dump OK: file="));
          Serial.print(filename);
          Serial.print(F(", start="));
          Serial.print(startAddr);
          Serial.print(F(", len="));
          Serial.println(len);
        #else
          Serial.write(kSerialNakByte);
          Serial.println(F("\rERROR: command j is only available in FPGA mode."));
        #endif
        break;
      default:
        Serial.print(F("\rERROR: unknown serial command: "));
        Serial.println(cmd);
        printSerialCommandsInfo();
        break;
    }
  }
}
